keeganmjgreen/3D-Printed-Sensors-Development-Platform/pdf/Creating-and-Modifying-Mask-Layouts-for-Sensor-Designs.pdf

# Creating and Modifying ‘Mask Layouts’ for Sensor Designs

Please refer to the ‘mask layouts’ of our sensor designs as a starting point. They have been provided as image templates.

1. Decide on the largest and/or most common/prevalent resolution expected for the mask layout. For example, 1 mm for most design features.
2. Estimate the bounding size of the mask layout. For example, layout height | = sensor width = 25
mm, layout width | = sensor length = 45 mm.
3. Using image editing software, create an image of height | pixels and width
pixels. Set its image resolution to | pixels, for reference. Keep in mind the
software units. For example:


4. Enable the pixel grid and rulers, if available. Using the grid will make the mask layout easier to draw.

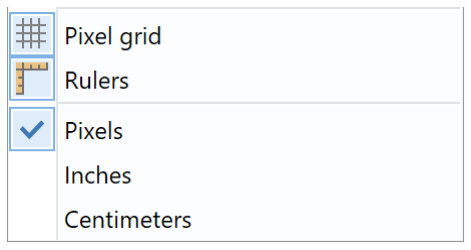
[picture p56: figure]

5. On a pixel scale, create the largest design features (of resolution | , that is) first. For example:

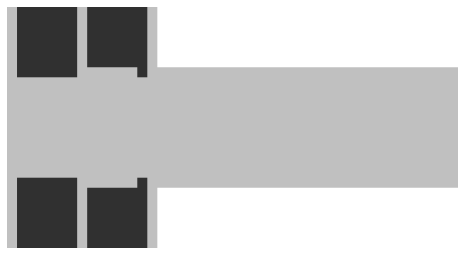
[picture p57: figure]

6. Resize the image to be of height | pixels and width | pixels, where
is the smallest underlying resolution. Update its image resolution to | pixels, for
reference, again. Keep in mind the software units. Use the nearest neighbor resampling method and maintain the aspect ratio. For example:


7. On the new pixel scale, create the smallest design features (of resolution , that is). For example:

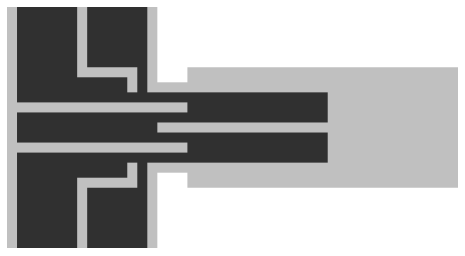
[picture p58: figure]

Tip: Use named image layers (as analogous to SolidWorks features). For example:
