keeganmjgreen/3D-Printed-Sensors-Development-Platform/pdf/Microcontroller-Based-Analog-Data-Logger-Interface.pdf

# Microcontroller-Based Analog Data Logger Interface

We developed a Windows 10 interface in Python for a microcontroller-based analog data logger with a wired connection to a computer. The program may be run directly by launching
[ Microcontroller_Based_Analog_Data_Logger_Interface.pyw ](https://raw.githubusercontent.com/keega
nmjgreen/3D-Printed-Sensors-Manual-Demo/main/Microcontroller_Based_Analog_Data_Logger_Interface.py
w) or, naturally, by executing the following command. (https://raw.githubusercontent.com/keeganmjgreen/3D-Printed-Sensors-Manual-Demo/main/Microcontroller_Based_Analog_Data_Logger_Interface.pyw)

Our interface is not real-time (beyond the sense that serial communication is not real-time). The logged data is plotted only after it is collected, not as it is collected. We are attempting to add this capability. Alternatively, or as a temporary workaround, we are adapting/using the Arduino IDE serial plotter and others.

The interface prompts you to connect the microcontroller (via USB) such as an Arduino if it has not already been connected, notifies that the device was connected, reads from the device over serial communication, and finally notifies that the device was disconnected (all Subsection 2). It then prepares the collected analog data (Subsection 3). Lastly, it makes the results accessible through a .CSV file generated in your working directory as well as an interactive, in-browser plot with export options (Subsection 4).
These features can be broken down by going through its library imports as follows.

# 1. Library Imports in Order of Appearance

The user is to at least be notified that the data logger was connected and disconnected (via USB). win10toast by Jithu Jacob is a Python library (PyPI, (https://pypi.org/project/win10toast/) GitHub) (https://github.com/jithurjacob/Windows-10-Toast-Notifications) for displaying Windows 10 toast notifications.

On the other hand, plyer.notification shows new notification senders for every notification sent.

For reasons that will become apparent, timer functionality is to be used. time is a standard Python library (Python documentation) (https://docs.python.org/3/library/time.html) for time access (and conversions, for that matter).

To read from the data logger, serial communication (https://en.wikipedia.org/wiki/Serial_communication) is to be used. pySerial by Chris Liechti is a Python library (PyPI, (https://pypi.org/project/pyserial/) GitHub, (https://github.com/pyserial/pyserial) documentation) (https://pyserial.readthedocs.io/en/latest/pyserial.html) that encapsulates access to computer serial ports, (https://en.wikipedia.org/wiki/Serial_port) including emulated ones such as those created by USB.

$ python Microcontroller_Based_Analog_Data_Logger_Interface.pyw

from win10toast import ToastNotifier

The received analog data is to be prepared before being made accessible.

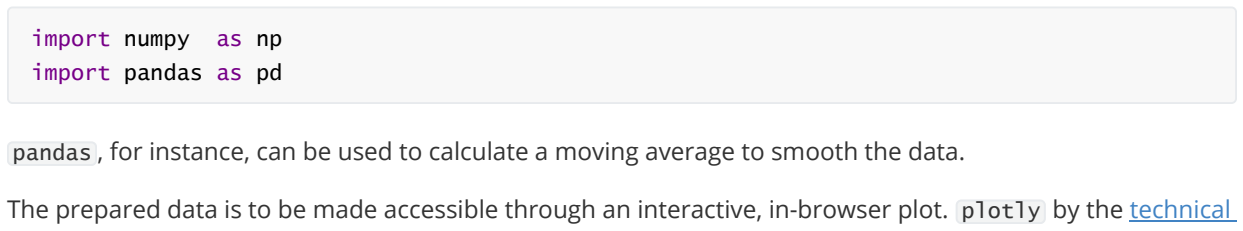
[picture p65: figure]
import numpy; import pandas as pd

pandas , for instance, can be used to calculate a moving average to smooth the data.

The prepared data is to be made accessible through an interactive, in-browser plot. plotly by the technical computing company of the same name is a Python library (PyPI, documentation) used to style interactive (https://plotly.com/) graphs.

# 2. Minimal User Interface | Reading from the Data Logger

To start with, initialize an instance of the toast notifier class using a memorable name:

This class has a show_toast method which is to be used. Among other arguments, it accepts a notification title , a notification msg , and an optional boolean specifying whether or not the showing of the notification (in its entire duration) is to be threaded (reference) (https://en.wikipedia.org/wiki/Thread_(computing)) with further Python instructions in this module (which calls show_toast ). We found that the notification message itself (not its title) is actually optional, being truly omitted by specifying msg to be a non-empty ‘empty’ string such as ' ' . Method show_toast returns a boolean representing whether a notification is sent successfully or not (i.e., if one is already being shown, at least from Python). We also found that initializing multiple instances of the ToastNotifier class does not allow multiple corresponding notifications to appear simultaneously in the same way.

Now, specify the chosen 9600 / 8-N-1 (https://en.wikipedia.org/wiki/8-N-1) serial communication (COM) (https://en.wikipedia.org/wiki/COM_(hardware_interface)) port:

Try to open this serial port with the assumption that the data logger has been connected to the computer

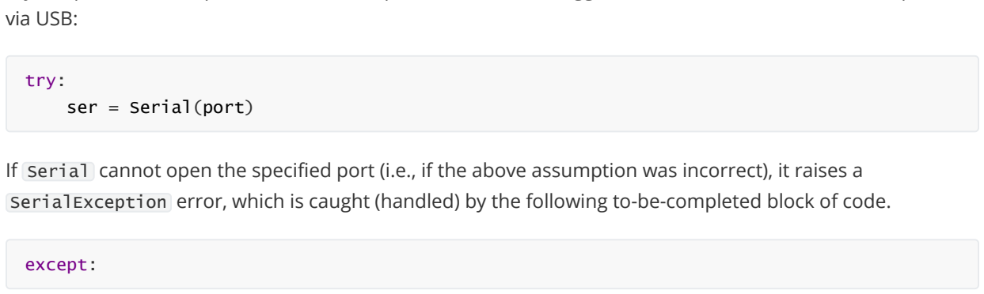
[picture p66: figure]
via USB:; try:; ser = Serial(port); except:

If Serial cannot open the specified port (i.e., if the above assumption was incorrect), it raises a SerialException error, which is caught (handled) by the following to-be-completed block of code.

from serial import Serial

import plotly.graph_objects as go

toaster = ToastNotifier()

port = 'COM4'

Now, we assume the general case that a system notification may already be present. As such, keep trying to…
show the user a prompt to connect to the microcontroller-based data logger, or open the serial port assuming that the device has since been connected,

whichever happens first (that is, whichever the program encounters first):

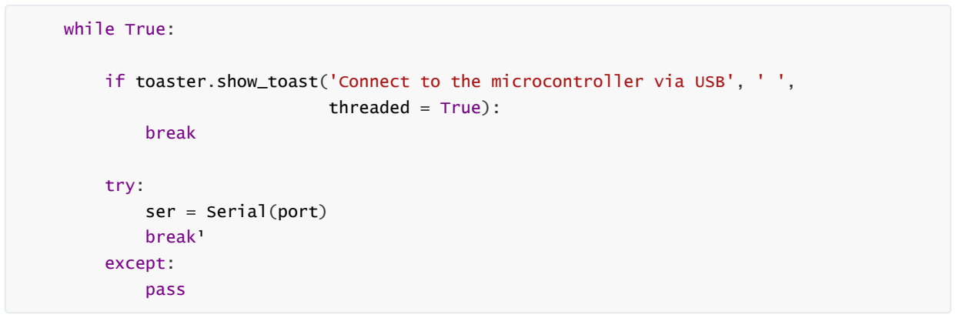
[picture p67: figure]
while True:; threaded = True):; break; try:; ser = Serial(port); break¹; except:; pass

¹ This break will not be reached unless the previous line, ser = Serial(port) , succeeds.
At least in this context, break and pass specifically mean ‘stop trying’ and ‘skip error handling’, respectively.

The first possible notification.

The device may have been connected by this point, in which case the connection prompt would be withheld.

Now, check if the ser object is defined (i.e., if the serial port was opened):

If not, keep trying to open the port assuming that the device will be connected:

if toaster.show_toast('Connect to the microcontroller via USB', ' ',

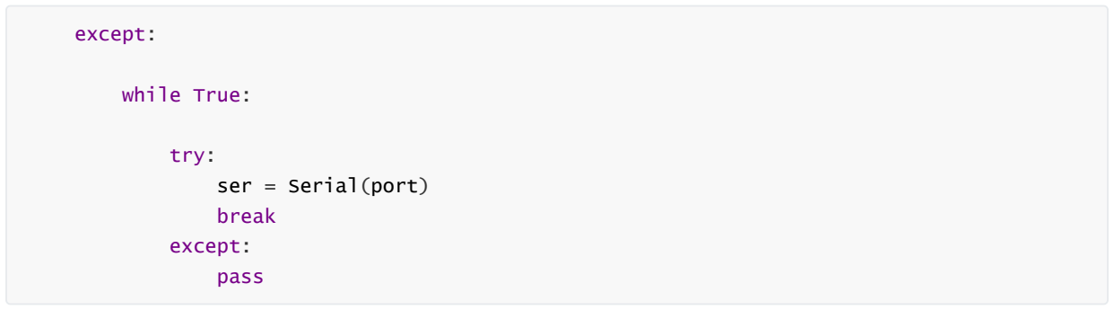
[picture p68: figure]
except:; while True:; try:; ser = Serial(port); break; except: pass

The data logger has been connected by this point, with or without a prompt to the user.
A notification that the device was connected is to be sent. We assume that an arbitrary notification may already be present, including but by no means limited to the connection prompt from before. If this is the case, it would delay the notification that the device was connected until ‘timing out’ (for lack of a better term). With this kind of notification, the user should know the time since its corresponding event actually

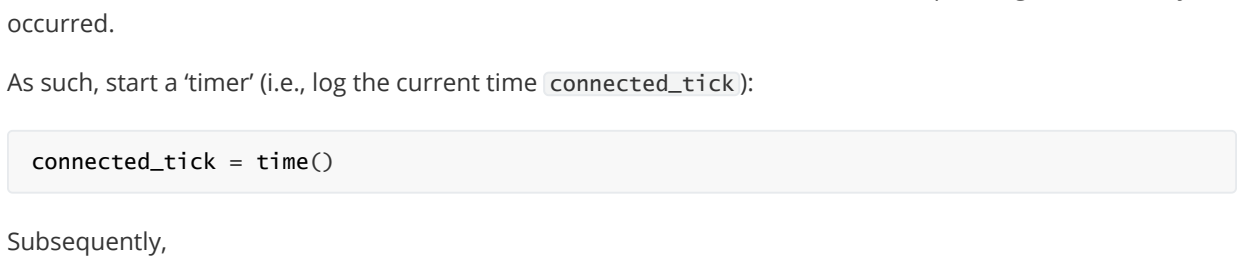
[picture p69: figure]
occurred.; Subsequently,; connected_tick = time()

As such, start a ‘timer’ (i.e., log the current time connected_tick ):

keep updating the suspected end time connected_tock and the elapsed time calculated from it, keep trying to show a notification that the microcontroller-based data logger was connected and of how long ago this event actually occurred,
and
keep checking if the serial port can be read from (i.e., if the device was not since disconnected),

all until the notification is sent:

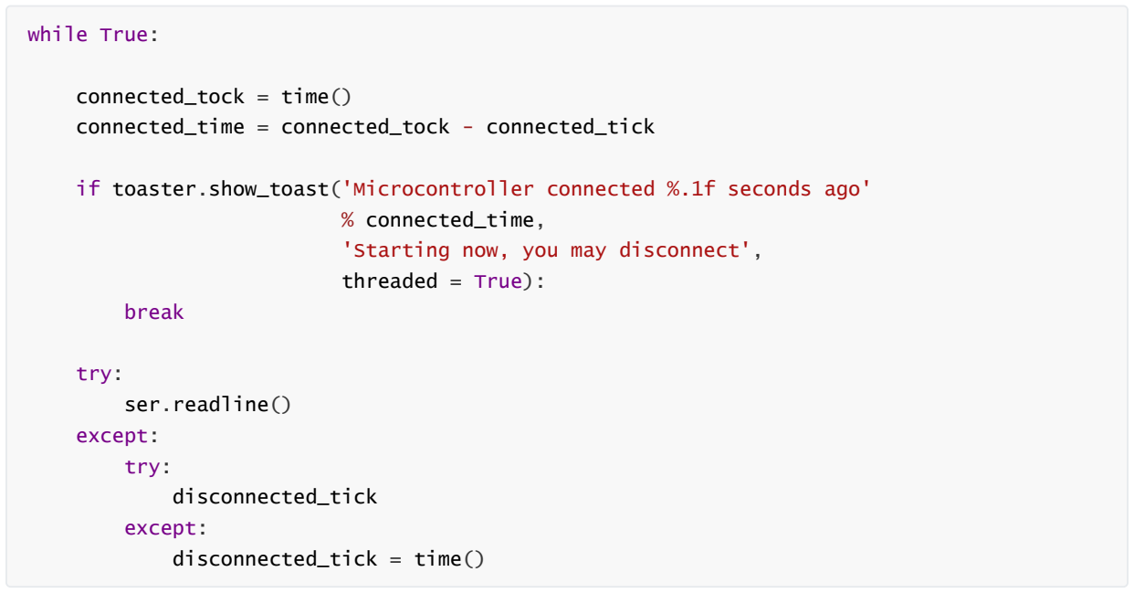
[picture p70: figure]
while True:; connected_tock = time(); connected_time = connected_tock - connected_tick; % connected_time,; 'Starting now, you may disconnect',; threaded = True):; break; try:; ser.readline(); except:; disconnected_tick except:; disconnected_tick = time()
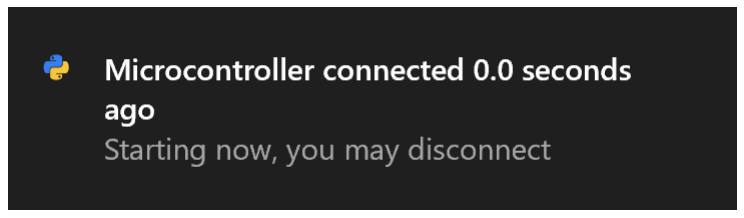
[picture p71: figure]

The second possible notification.

if toaster.show_toast('Microcontroller connected %.1f seconds ago'

The user would be ‘permitted’ to disconnect the device as soon as it is connected if the previous busy waiting while loop is manually (albeit awkwardly) threaded with the upcoming data logging one, or if (https://en.wikipedia.org/wiki/Busy_waiting) done using the threading standard Python module (documentation) (https://docs.python.org/3/library/threading.html) instead. However, the user should know not when the device is simply plugged in (as they do and need not be notified), but when the serial communication link is established soon thereafter.

Now, initialize an empty list of lines to be read from the serial port, assuming that it is still open:

Keep trying to read ASCII (https://en.wikipedia.org/wiki/ASCII) characters from the serial port, and add them to the list of lines thereof, until the port is no longer open (i.e., until the device is disconnected):

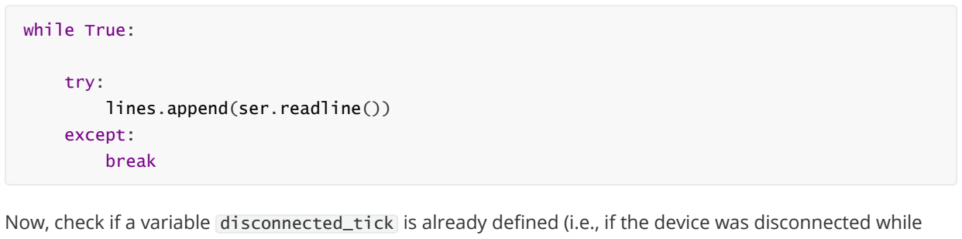
[picture p72: figure]
while True:; try:; lines.append(ser.readline()); except: break

Now, check if a variable disconnected_tick is already defined (i.e., if the device was disconnected while waiting to send the previous notification):

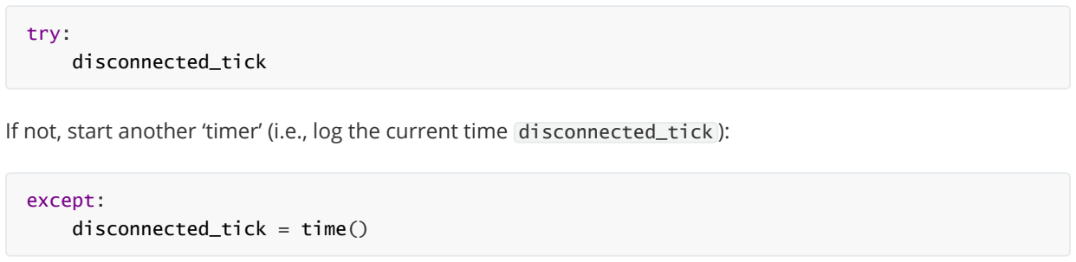
[picture p73: figure]
try:; disconnected_tick; except:; disconnected_tick = time()

If not, start another ‘timer’ (i.e., log the current time disconnected_tick ):

Keep trying to show a notification that the microcontroller-based data logger was disconnected, and of how long ago this event actually occurred:

lines = []

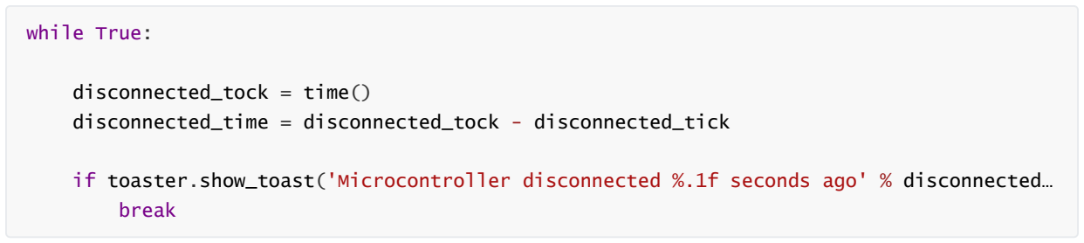
[picture p74: figure]
while True:; disconnected_tock = time(); disconnected_time = disconnected_tock - disconnected_tick; break

if toaster.show_toast('Microcontroller disconnected %.1f seconds ago' % disconnected…

The third possible notification.

# 3. Preparing the Collected Analog Data

See the following numbered, broken-down block of code.
Now,
1. Trim the last two line-ending ASCII characters: line feed <LF> b'\n' and carriage return <CR> b'\r' .
2. Typecast (convert) the remaining ASCII characters from a byte literal to a float.
3. Do the above for all lines but the first one, which may have been cut off.
This is a list comprehension. (https://docs.python.org/3/tutorial/datastructures.html#list-comprehensions)
4. From the list, construct a NumPy ndarray , , which is a time series (https://en.wikipedia.org/wiki/Time_series) of logged data.

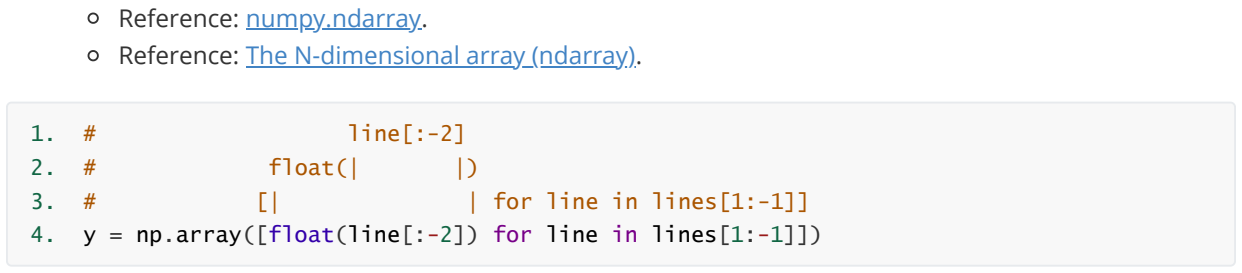
[picture p75: figure]
Reference: numpy.ndarray. Reference: The N-dimensional array (ndarray).; line[:-2]; float(│; │ for line in lines[1:-1]]

Specify the scalar time interval between data points and generate a time array, , corresponding to them:

Specify a moving average window and use it to smooth the data:

# 4. Making the Results Accessible

Firstly, export the prepared data to a CSV file for reference:

4. y = np.array([float(line[:-2]) for line in lines[1:-1]])

y_smooth = pd.Series(y).rolling(window, center = True).mean().to_numpy()

np.savetxt('data.csv', y, fmt = '%.2f')

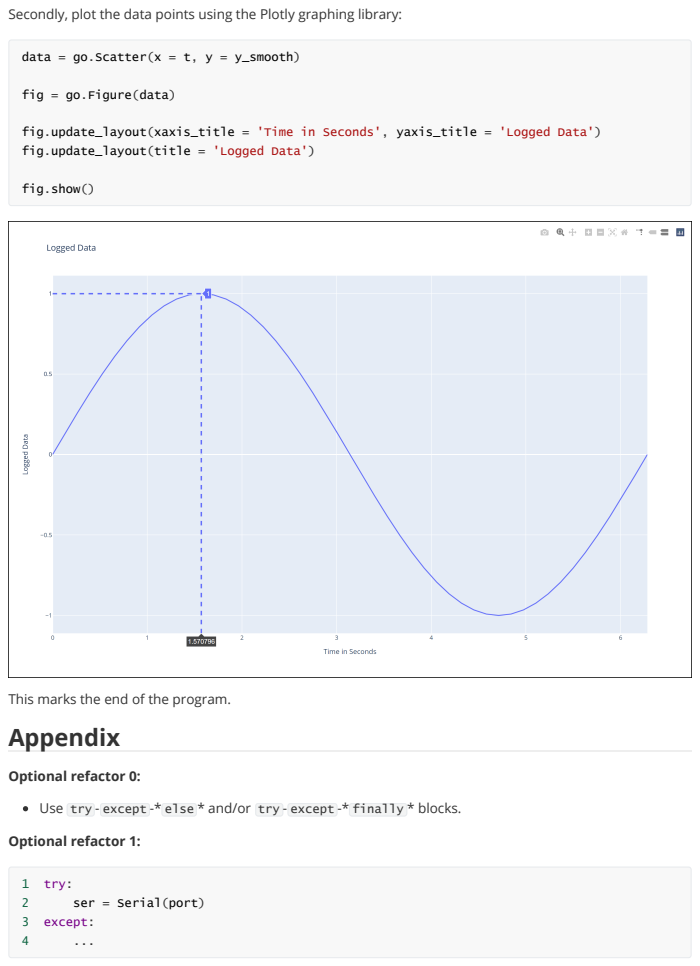
[picture p76: page 7]
Optional refactor 0:; fig.show(); try:; ser = Serial(port); except:

Secondly, plot the data points using the Plotly graphing library:

data = go.Scatter(x = t, y = y_smooth)

fig = go.Figure(data)

fig.update_layout(xaxis_title = 'Time in Seconds', yaxis_title = 'Logged Data')
fig.update_layout(title = 'Logged Data')

This marks the end of the program.
Appendix

Use try - except -* else * and/or try - except -* finally * blocks.
Optional refactor 1:

to

However, between lines 3 and 4 above, the serial port might become unavailable, in which case Serial would throw an uncaught SerialException error.
Optional refactor 2:

to

1 from serial.tools.list_ports import comports
2
3 | if port in [comport.device for comport in comports()]:
4 | ser = Serial(port)
5 | elif:
6 | ...
1 | try:
2 | ser.readline()
3 | except:
4 | ...
1 | from serial.tools.list_ports import comports
2
3 | if port not in [comport.device for comport in comports()]:
4 | ...
