keeganmjgreen/3D-Printed-Sensors-Development-Platform/Development-Kit/Pithon Force Sensor, Accelerometer/mid_str_4T_sensing_1_and_elem-Render.png

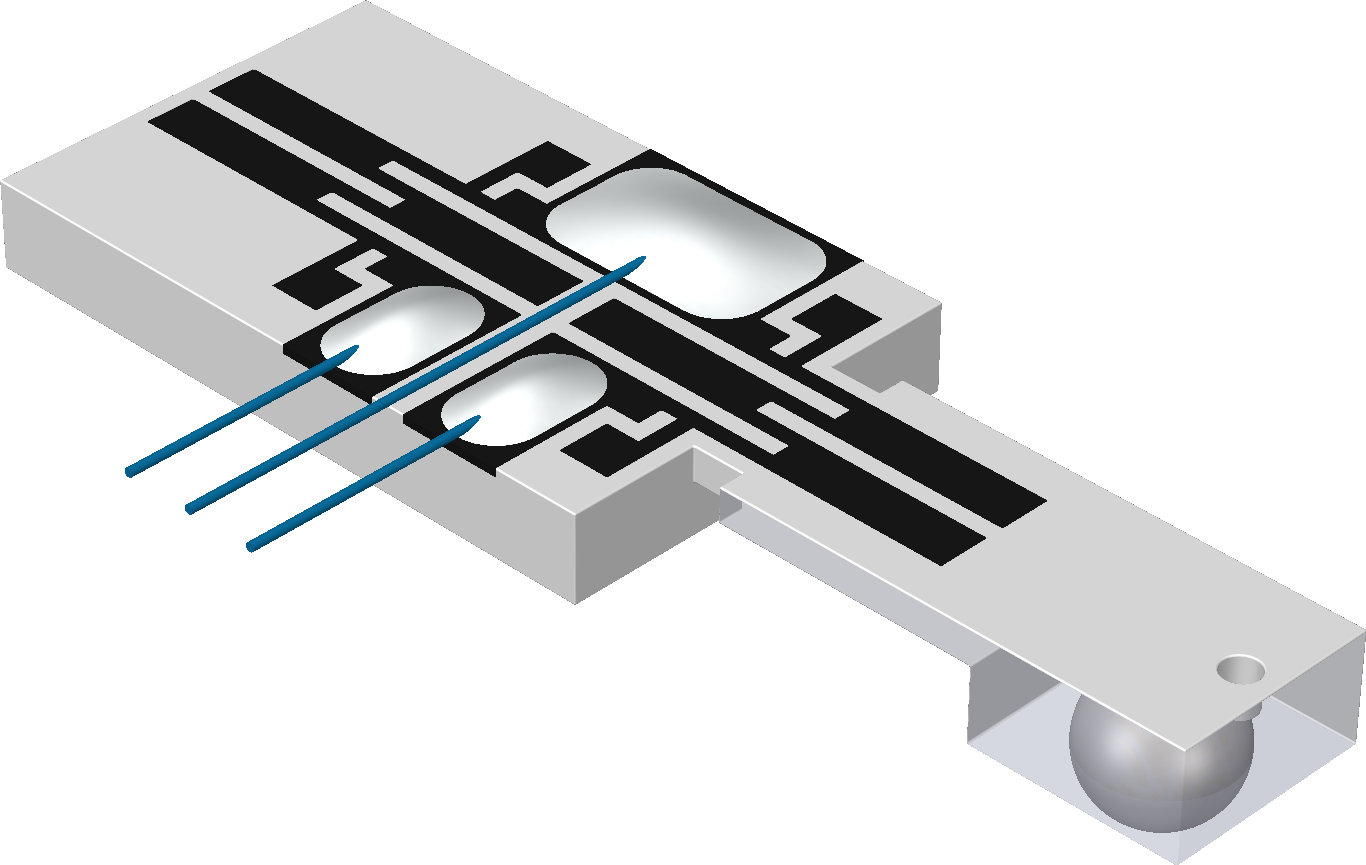
Development-Kit/Pithon Force Sensor, Accelerometer/mid_str_4T_sensing_1_and_elem-Render.png
