keeganmjgreen/3D-Printed-Sensors-Development-Platform/img/Example-Process-Flow/Figure (7.5).png

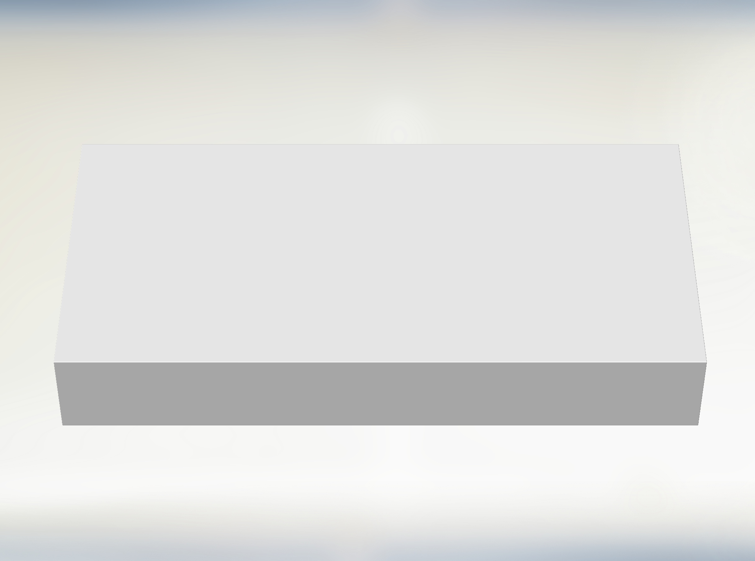
img/Example-Process-Flow/Figure (7.5).png
