keeganmjgreen/3D-Printed-Sensors-Development-Platform/img/Example-Process-Flow/Figure (15).png

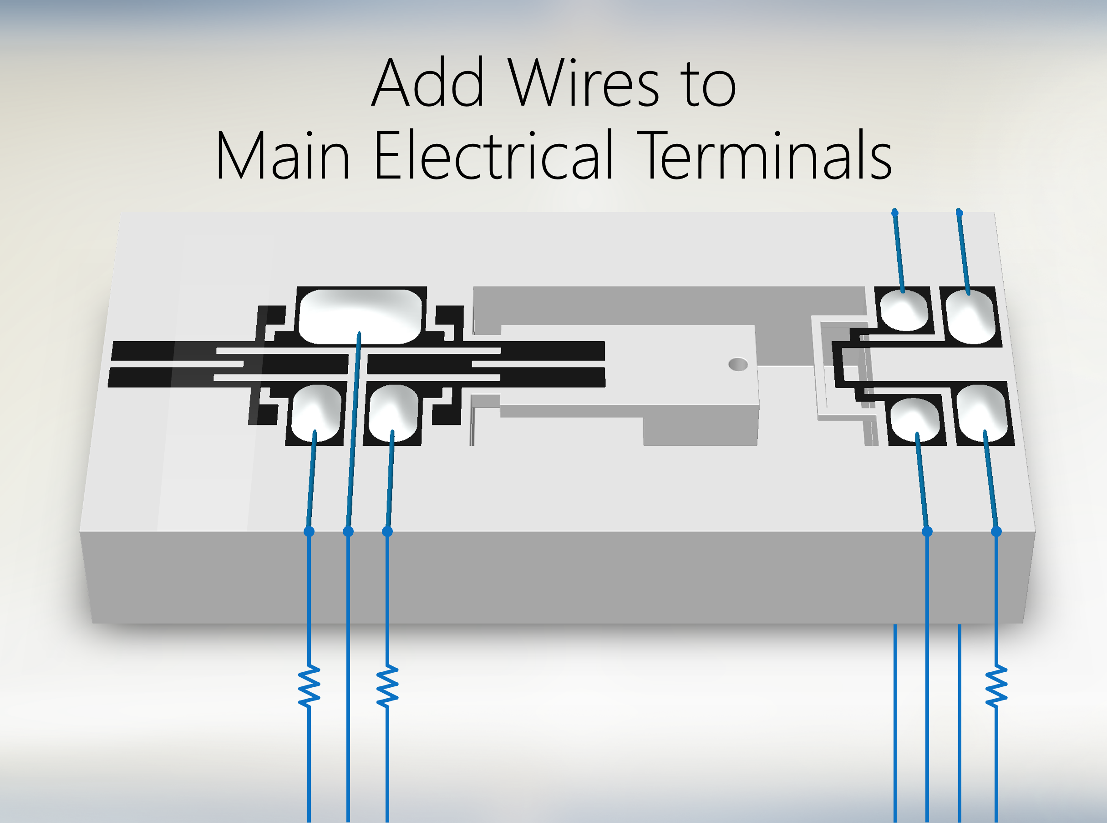
img/Example-Process-Flow/Figure (15).png
