keeganmjgreen/3D-Printed-Sensors-Development-Platform/img/Preparing-Electrical-Contacts/Cantilever-Face-Up.jpg

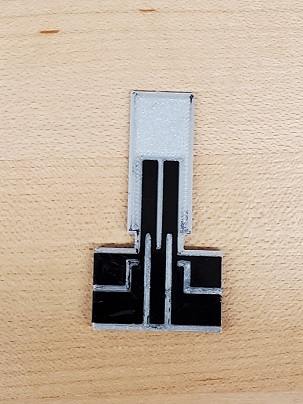
img/Preparing-Electrical-Contacts/Cantilever-Face-Up.jpg
