keeganmjgreen/3D-Printed-Sensors-Development-Platform/Development-Kit/Pithon Temperature Sensor/temp_4T_sensing_1.STL

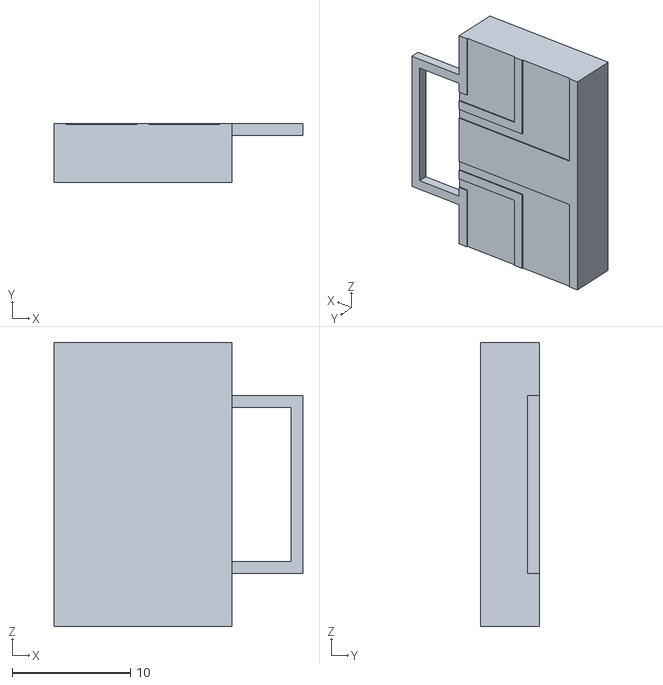
[picture p102: CAD file, 2021-09-01]
Development-Kit/Pithon Temperature Sensor/temp_4T_sensing_1.STL
21.0 x 5.00 x 24.0
